newdigate/teensy-control-voltage/hardware/boards/3d/ACJS-MV35-5.step

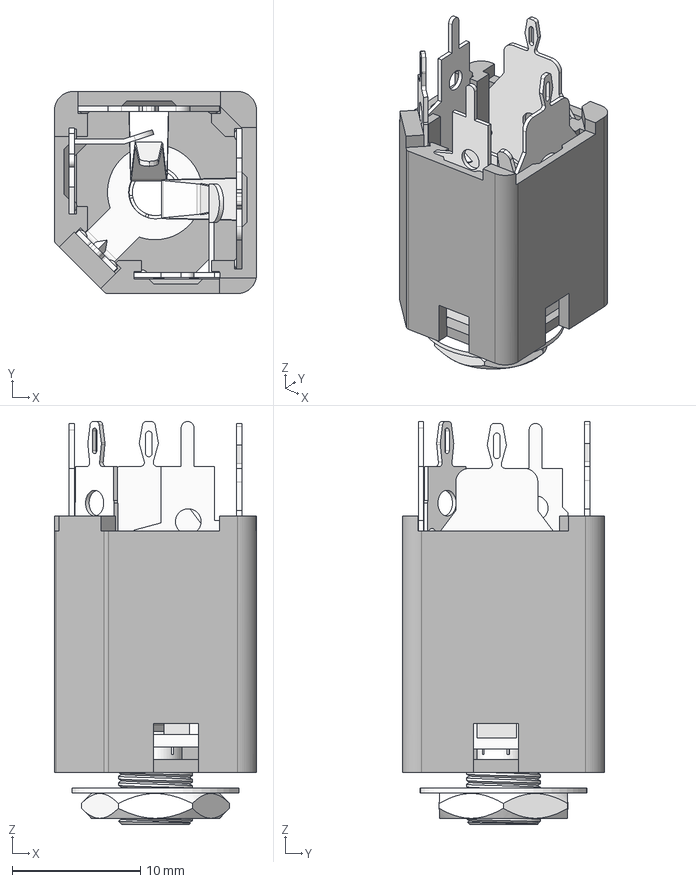
[picture p17: CAD file, 2020-09-20]
hardware/boards/3d/ACJS-MV35-5.step
15.8 x 15.8 x 31.4 mm
