newdigate/teensy-control-voltage/hardware/boards/3d/ZX62-AB-5PA.stp

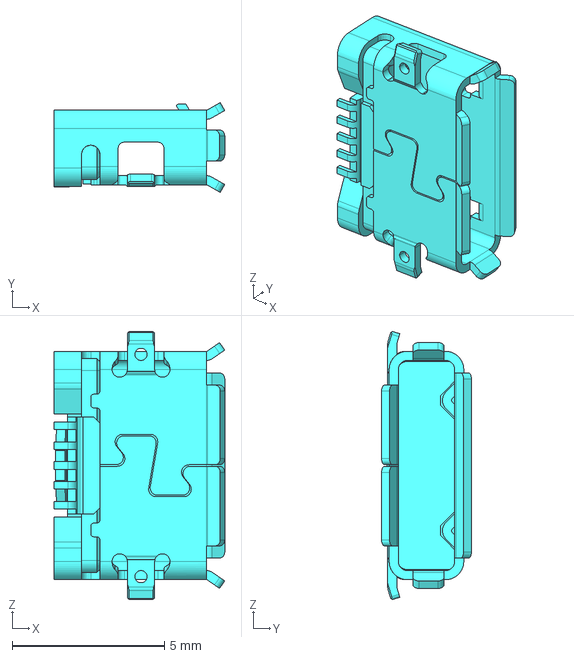
[picture p18: CAD file, 2020-09-20]
hardware/boards/3d/ZX62-AB-5PA.stp
5.60 x 2.95 x 8.80 mm
