newdigate/teensy-control-voltage/hardware/boards/3d/User Library-8-pin-DIP_GW_HCPL-4200-300E.STEP

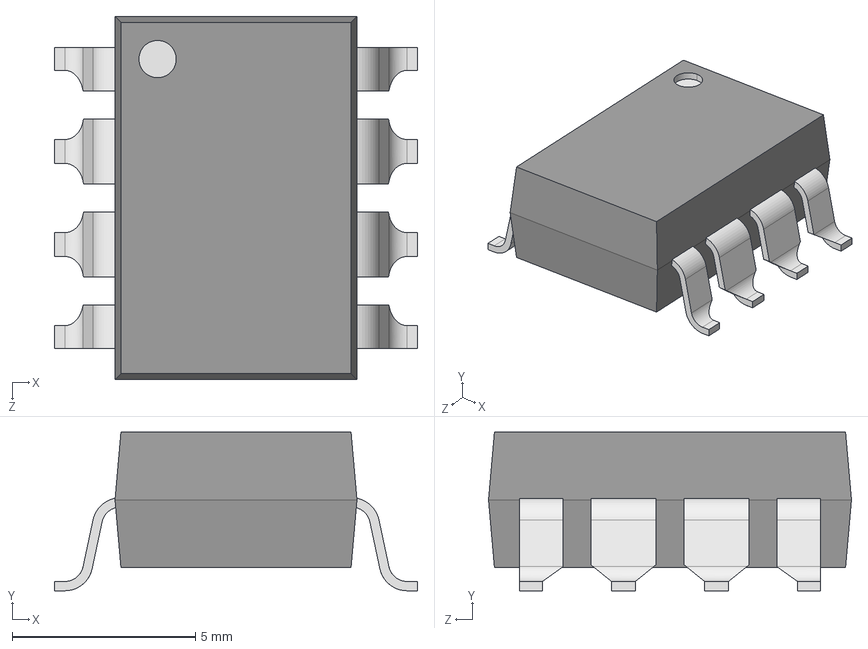
[picture p19: CAD file, 2020-09-20]
hardware/boards/3d/User Library-8-pin-DIP_GW_HCPL-4200-300E.STEP
9.90 x 4.33 x 9.90 mm
