newdigate/teensy-control-voltage/hardware/boards/3d/HFW8R-1STE1LF.stp

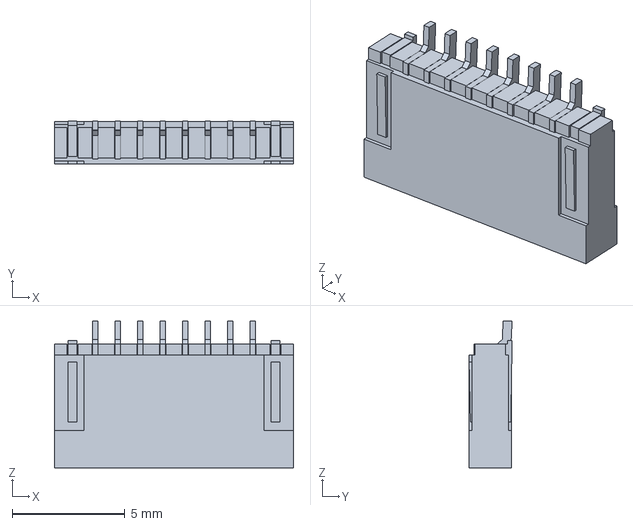
[picture p20: CAD file, 2020-09-20]
hardware/boards/3d/HFW8R-1STE1LF.stp
10.6 x 1.92 x 6.50 mm
